IamMrCupp/pcie-gpu-test-rig/wiring/pcie_rig_power.kicad_sch

## KiCad design wiring/pcie_rig_power.kicad_sch (2026-10-01)

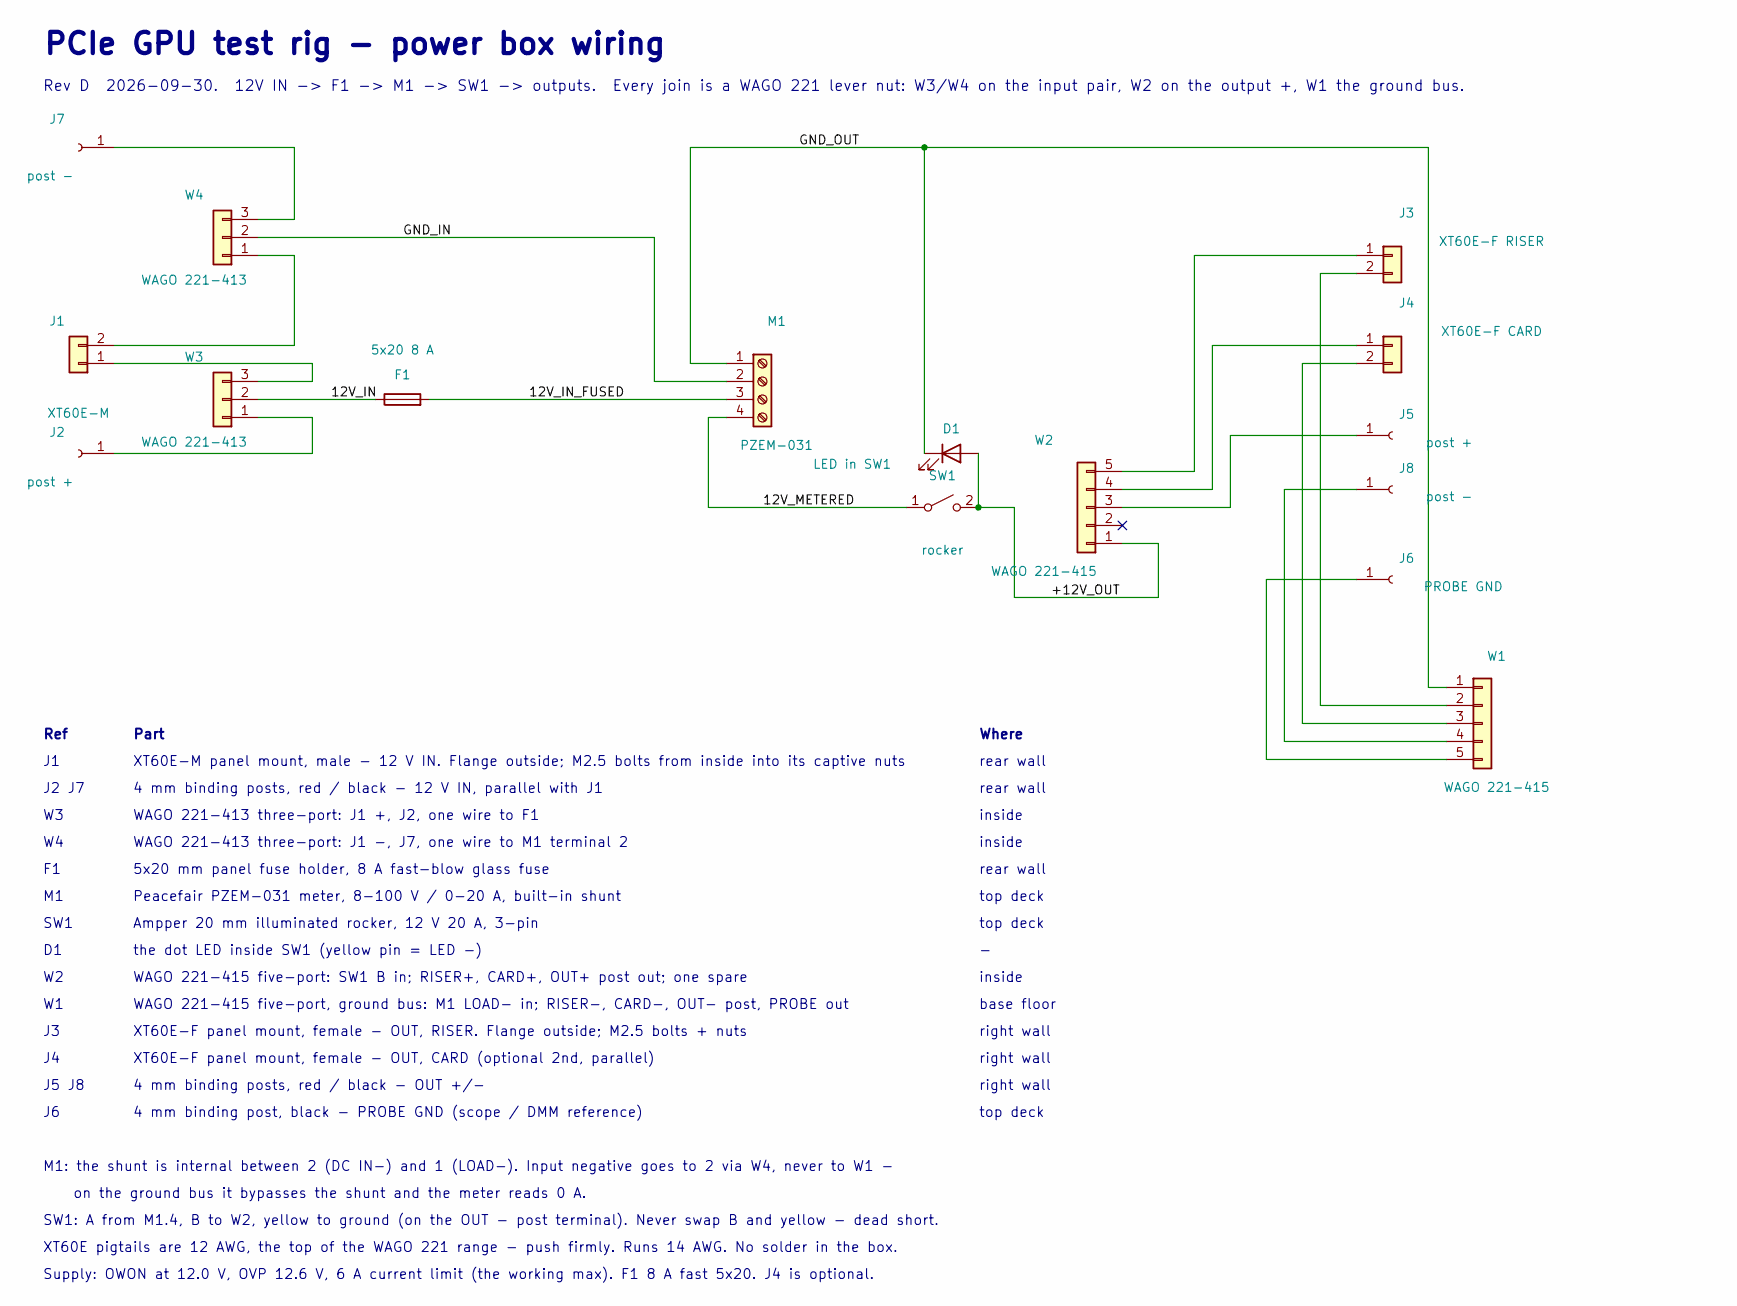
[picture p2: schematic pcie_rig_power.kicad_sch]

Parts:
D1: LED in SW1
F1: 5x20 8 A
J1: XT60E-M
J2, J5: post +
J3: XT60E-F RISER
J4: XT60E-F CARD
J6: PROBE GND
J7, J8: post -
M1: PZEM-031
SW1: rocker
W1, W2: WAGO 221-415
W3, W4: WAGO 221-413

Connections:
12V_IN: F1.1, W3.2
12V_IN_FUSED: F1.2, M1.3
12V_METERED: M1.4, SW1.1 (A)
+12V_OUT: D1.2 (A), SW1.2 (B), W2.1
GND_IN: M1.2, W4.2
GND_OUT: D1.1 (K), M1.1, W1.1
unnamed: J1.1, W3.3
unnamed: J1.2, W4.1
unnamed: J2.1, W3.1
unnamed: J3.1, W2.5
unnamed: J3.2, W1.2
unnamed: J4.1, W2.4
unnamed: J4.2, W1.3
unnamed: J5.1, W2.3
unnamed: J6.1, W1.5
unnamed: J7.1, W4.3
unnamed: J8.1, W1.4

Notes on the sheet:
PCIe GPU test rig - power box wiring
Rev D 2026-09-30. 12V IN -> F1 -> M1 -> SW1 -> outputs. Every join is a WAGO 221 lever nut: W3/W4 on the input pair, W2 on the output +, W1 the ground bus.
Ref
Part
Where
XT60E-M panel mount, male - 12 V IN. Flange outside; M2.5 bolts from inside into its captive nuts
rear wall
J2 J7
4 mm binding posts, red / black - 12 V IN, parallel with J1
WAGO 221-413 three-port: J1 +, J2, one wire to F1
inside
WAGO 221-413 three-port: J1 -, J7, one wire to M1 terminal 2
5x20 mm panel fuse holder, 8 A fast-blow glass fuse
Peacefair PZEM-031 meter, 8-100 V / 0-20 A, built-in shunt
top deck
SW1
Ampper 20 mm illuminated rocker, 12 V 20 A, 3-pin
the dot LED inside SW1 (yellow pin = LED -)
WAGO 221-415 five-port: SW1 B in; RISER+, CARD+, OUT+ post out; one spare
WAGO 221-415 five-port, ground bus: M1 LOAD- in; RISER-, CARD-, OUT- post, PROBE out
base floor
XT60E-F panel mount, female - OUT, RISER. Flange outside; M2.5 bolts + nuts
right wall
XT60E-F panel mount, female - OUT, CARD (optional 2nd, parallel)
J5 J8
4 mm binding posts, red / black - OUT +/-
4 mm binding post, black - PROBE GND (scope / DMM reference)
M1: the shunt is internal between 2 (DC IN-) and 1 (LOAD-). Input negative goes to 2 via W4, never to W1 -
on the ground bus it bypasses the shunt and the meter reads 0 A.
SW1: A from M1.4, B to W2, yellow to ground (on the OUT - post terminal). Never swap B and yellow - dead short.
XT60E pigtails are 12 AWG, the top of the WAGO 221 range - push firmly. Runs 14 AWG. No solder in the box.
Supply: OWON at 12.0 V, OVP 12.6 V, 6 A current limit (the working max). F1 8 A fast 5x20. J4 is optional.
